ClusterM/nes2wii/wm_crypto.h

#ifndef wm_crypto_h

#include <avr/pgmspace.h>

/*

I'd like to thank Hector Martin for posting his encryption method!
His website is http://www.marcansoft.com/
Decryption method found at http://www.derkeiler.com/pdf/Newsgroups/sci.crypt/2008-11/msg00110.pdf

*/

const unsigned char ans_tbl[7][6] PROGMEM = {
	{0xA8,0x77,0xA6,0xE0,0xF7,0x43},
	{0x5A,0x35,0x85,0xE2,0x72,0x97},
	{0x8F,0xB7,0x1A,0x62,0x87,0x38},
	{ 0xD,0x67,0xC7,0xBE,0x4F,0x3E},
	{0x20,0x76,0x37,0x8F,0x68,0xB7},
	{0xA9,0x26,0x3F,0x2B,0x10,0xE3},
	{0x30,0x7E,0x90, 0xE,0x85, 0xA},
};

const unsigned char sboxes[10][256] PROGMEM = {
	{
		0x70,0x51,   3,0x86,0x40, 0xD,0x4F,0xEB,0x3E,0xCC,0xD1,0x87,0x35,0xBD,0xF5, 0xB,
		0x5E,0xD0,0xF8,0xF2,0xD5,0xE2,0x6C,0x31, 0xC,0xAD,0xFC,0x21,0xC3,0x78,0xC1,   6,
		0xC2,0x4C,0x55,0xE6,0x4A,0x34,0x48,0x11,0x1E,0xDA,0xE7,0x1A,0x84,0xA0,0x96,0xA7,
		0xE3,0x7F,0xAF,0x63,0x9C,0xFA,0x23,0x5B,0x79,0xC8,0x9E,0xBA,0xB2,0xC9,0x22,0x12,
		0x4B,0xB3,0xA1,0xB6,0x32,0x49,0xA2,0xE1,0x89,0x39,0x10,0x66,0xC5,   7,0x8F,0x54,
		0xEA,0x91,0xCA,0x3F,0xF9,0x19,0xF0,0xD7,0x46,0xBC,0x28,0x1B,0x61,0xE8,0x2F,0x6A,
		0xAE,0x9D,0xF6,0x4E,   9,0x14,0x77,0x4D,0xDB,0x1F,0x2E,0x7B,0x7C,0xF1,0x43,0xA3,
		   0,0xB8,0x13,0x8C,0x85,0xB9,0x29,0x75,0x88,0xFD,0xD2,0x56,0x1C,0x50,0x97,0x41,
		0xE5,0x3B,0x60,0xB5,0xC0,0x64,0xEE,0x98,0xD6,0x2D,0x25,0xA4,0xAA,0xCD,0x7D,0xA8,
		0x83,0xC6,0xAB,0xBE,0x44,0x99,0x26,0x3C,0xCE,0x9F,0xBF,0xD3,0xCB,0x76,0x7A,0x7E,
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
		0x17,0x6A,0x89,0x4F,0x66,0x7F,0xC6,0x50,0x55,0x92,0x6F,0xBD,0xE7,0xD2,0x40,0x72,
		0x8D,0xBB,0xEC,   6,0x42,0x8A,0xE4,0x88,0x9D,0x7E,0x7A,0x82,0x27,0x13,0x41,0x1A,
		0xAF,0xC8,0xA4,0x76,0xB4,0xC2,0xFE,0x6D,0x1C,0xD9,0x61,0x30,0xB3,0x7C,0xEA,0xF7,
		0x29, 0xF,0xF2,0x3B,0x51,0xC1,0xDE,0x5F,0xE5,0x2A,0x2F,0x99, 0xB,0x5D,0xA3,0x2B,
		0x4A,0xAB,0x95,0xA5,0xD3,0x58,0x56,0xEE,0x28,0x31,   0,0xCC,0x15,0x46,0xCA,0xE6,
		0x86,0x38,0x3C,0x65,0xF5,0xE3,0x9F,0xD6,0x5B,   9,0x49,0x83,0x70,0x2D,0x53,0xA9,
		0x7D,0xE2,0xC4,0xAC,0x8E,0x5E,0xB8,0x25,0xF4,0xB9,0x57,0xF3,0xF1,0x68,0x47,0xB2,
		0xA2,0x59,0x20,0xCE,0x34,0x79,0x5C,0x90, 0xE,0x1E,0xBE,0xD5,0x22,0x23,0xB1,0xC9,
		0x18,0x62,0x16,0x2E,0x91,0x3E,   7,0x8F,0xD8,0x3F,0x93,0x3D,0xD4,0x9B,0xDF,0x85,
		0x21,0xFB,0x11,0x74,0x97,0xC7,0xD7,0xDC,0x4C,0x19,0x45,0x98,0xE9,0x43,   2,0x4B,
		0xBC,0xC3,   4,0x9C,0x6B,0xF0,0x75,0x52,0xA7,0x26,0xF6,0xC5,0xBA,0xCF,0xB0,0xB7,
		0xAE,0x5A,0xA1,0xBF,   3,0x8B,0x80,0x12,0x6E, 0xC,0xEB,0xF9,0xC0,0x44,0x24,0xEF,
		0x10,0xF8,0xA8,0x8C,0xE8,0x7B,0xFF,0x9E,0x2C,0xCD,0x60,0x36,0x87,0xB5,0x94,0xA6,
		0x54,0x73,0x3A,0x14,0x4E,   1,0x1D,0xB6,0xFD,0x37,0x48,0x4D,0x39,0xCB,0xE0,0x32,
	}
};

#define wm_crypto_h
#endif
